Kunkles/bike-ramp/deck/base_6a.stl

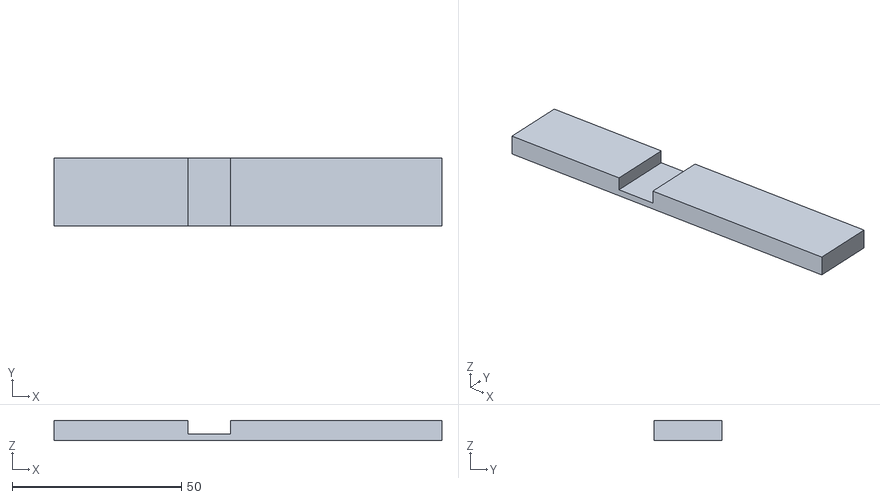
[picture p18: CAD file, 2026-08-14]
deck/base_6a.stl
114.6 x 20.0 x 6.00
