Kunkles/bike-ramp/stl/tile_11.stl

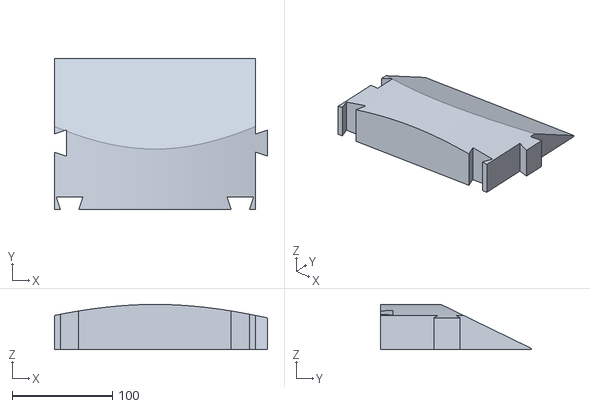
[picture p19: CAD file, 2026-08-17]
stl/tile_11.stl
212.0 x 150.0 x 45.0
