Kunkles/bike-ramp/stl/tile_21.stl

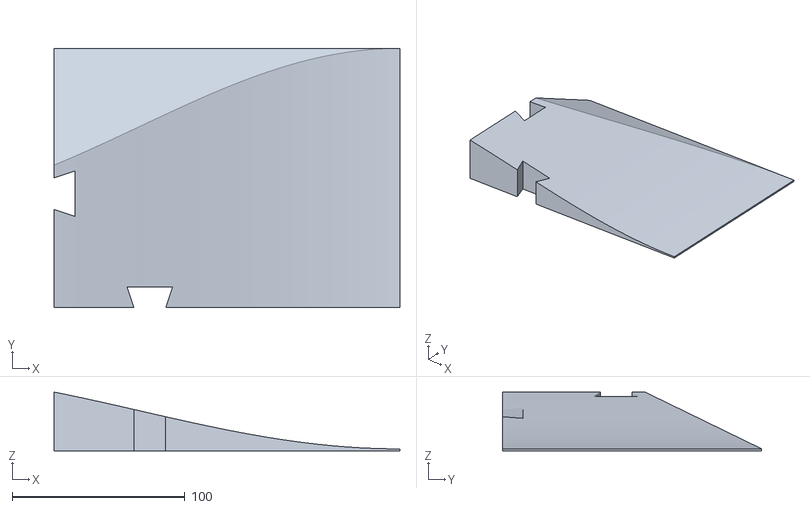
[picture p20: CAD file, 2026-08-17]
stl/tile_21.stl
200.0 x 150.0 x 34.0
