Kunkles/bike-ramp/deck/channel_0R.stl

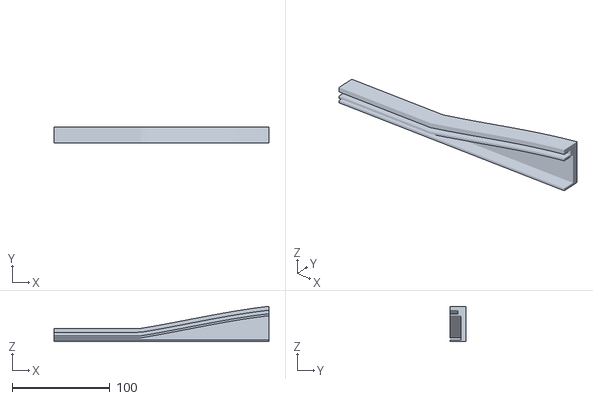
[picture p21: CAD file, 2026-08-14]
deck/channel_0R.stl
220.0 x 16.0 x 36.3
