Kunkles/bike-ramp/deck/base_1c.stl

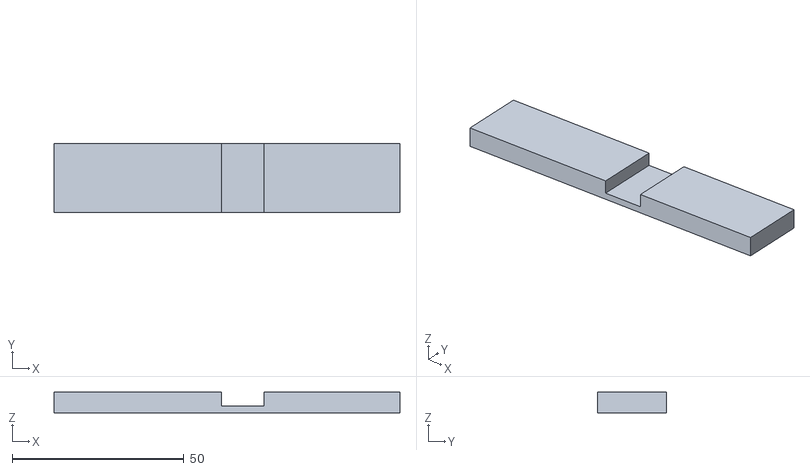
[picture p22: CAD file, 2026-08-14]
deck/base_1c.stl
100.8 x 20.0 x 6.00
