Kunkles/bike-ramp/deck/channel_1L.stl

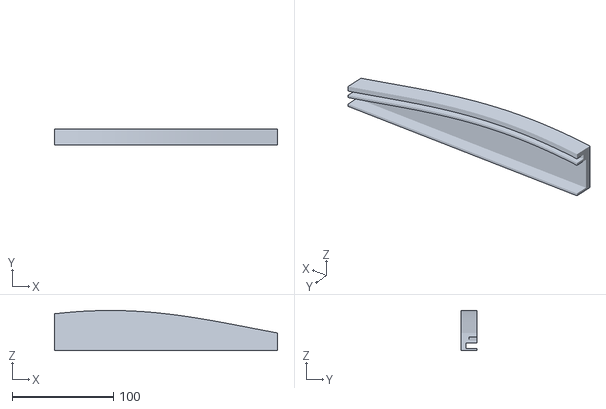
[picture p23: CAD file, 2026-08-14]
deck/channel_1L.stl
220.0 x 16.0 x 39.5
