Kunkles/bike-ramp/deck/rib_03.stl

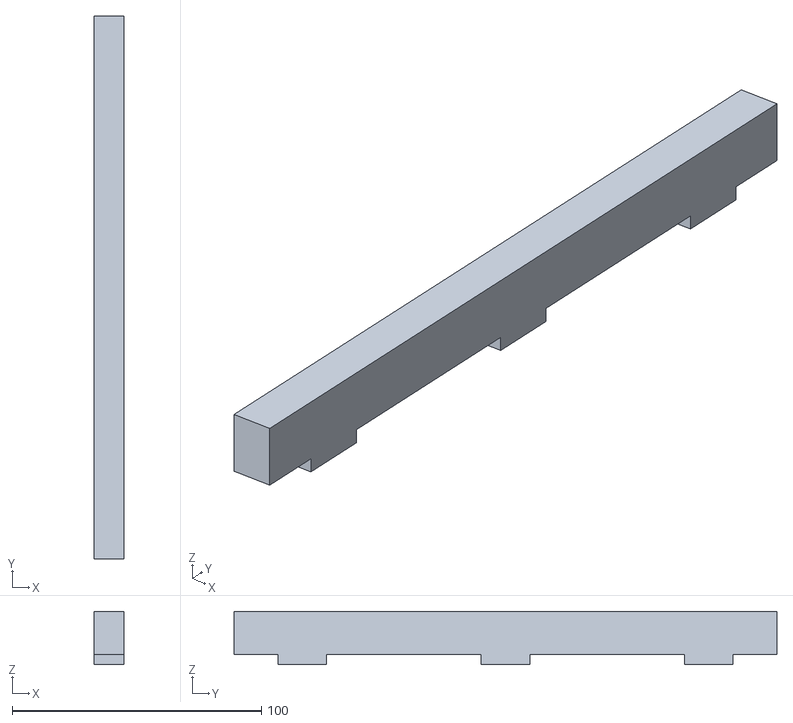
[picture p24: CAD file, 2026-08-14]
deck/rib_03.stl
12.0 x 218.0 x 21.3
