Kunkles/bike-ramp/deck/rib_01.stl

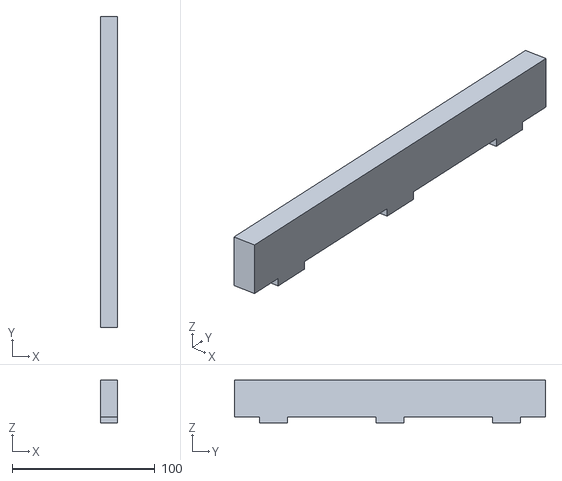
[picture p25: CAD file, 2026-08-14]
deck/rib_01.stl
12.0 x 218.0 x 29.8
