Kunkles/bike-ramp/deck/channel_2R.stl

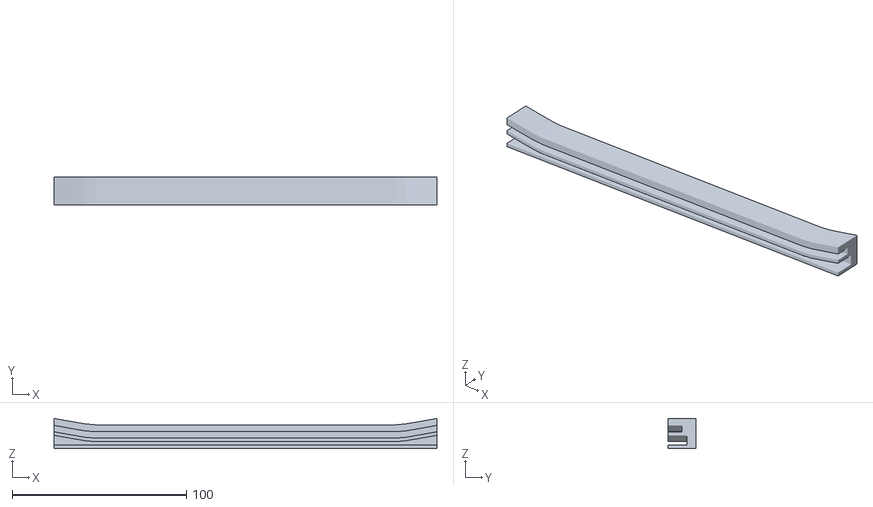
[picture p26: CAD file, 2026-08-14]
deck/channel_2R.stl
220.0 x 16.0 x 17.3
